tebl/RC1802-Cosmac-ELF/Gallery/1802_ui_d2.PNG

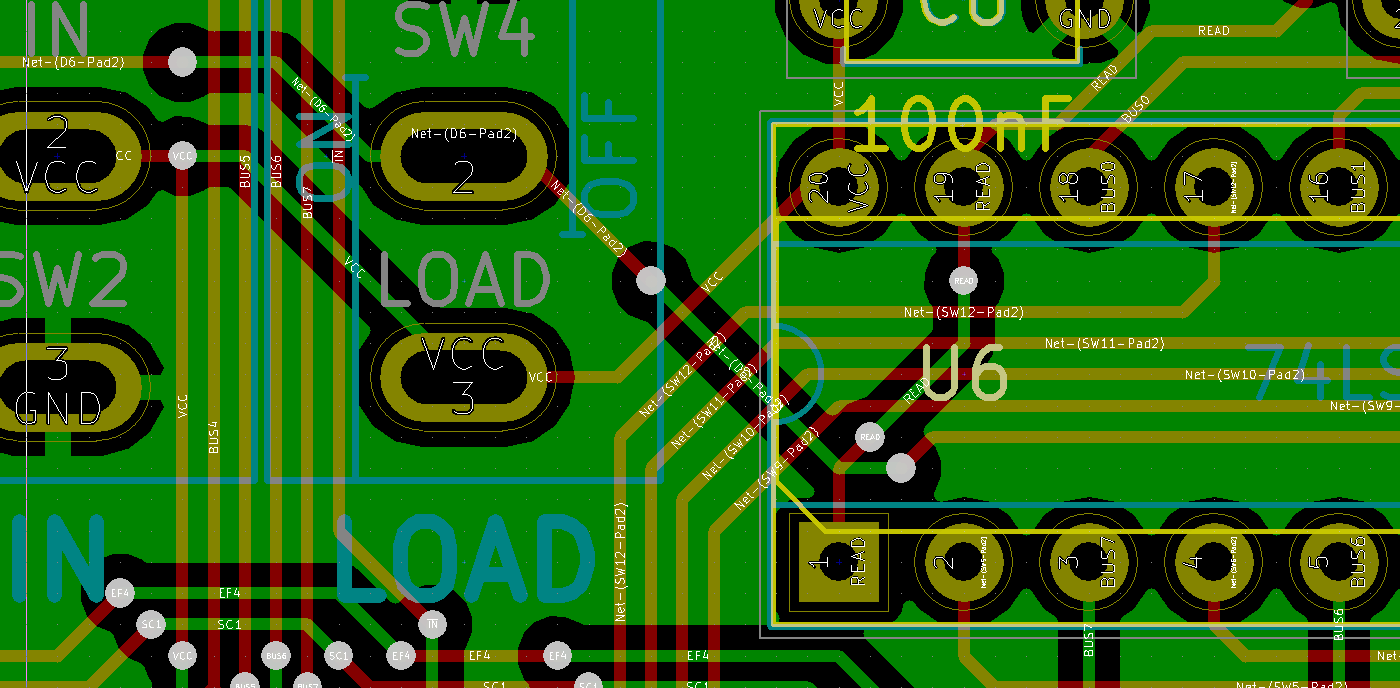
Gallery/1802_ui_d2.PNG
