tebl/RC1802-Cosmac-ELF/Gallery/Loopback_000.jpg

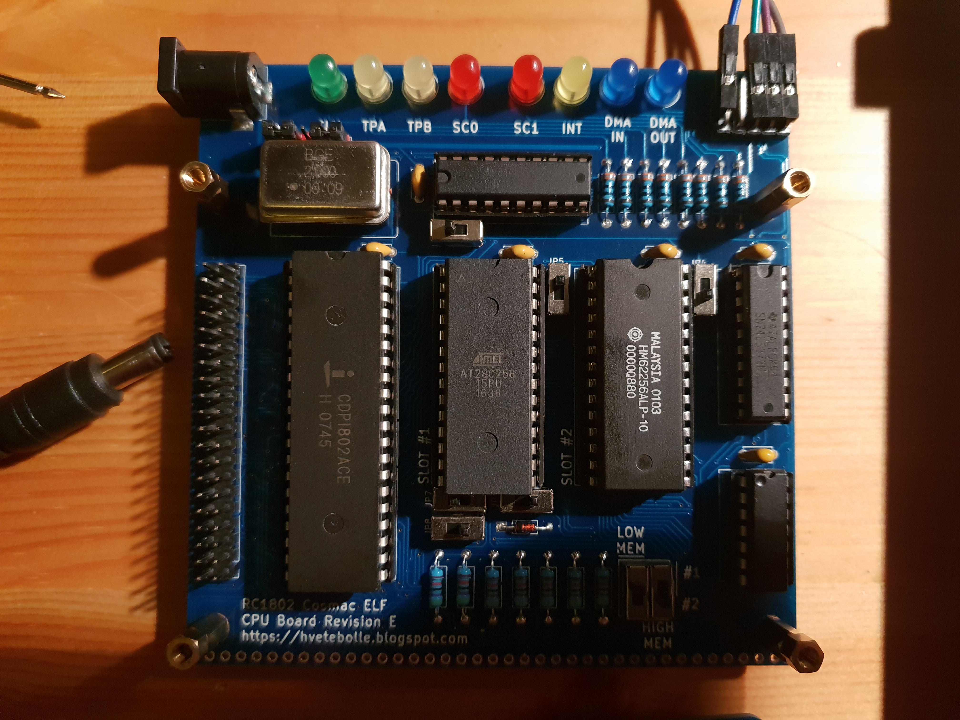
Gallery/Loopback_000.jpg
