tebl/RC1802-Cosmac-ELF/Gallery/Loopback_001.jpg

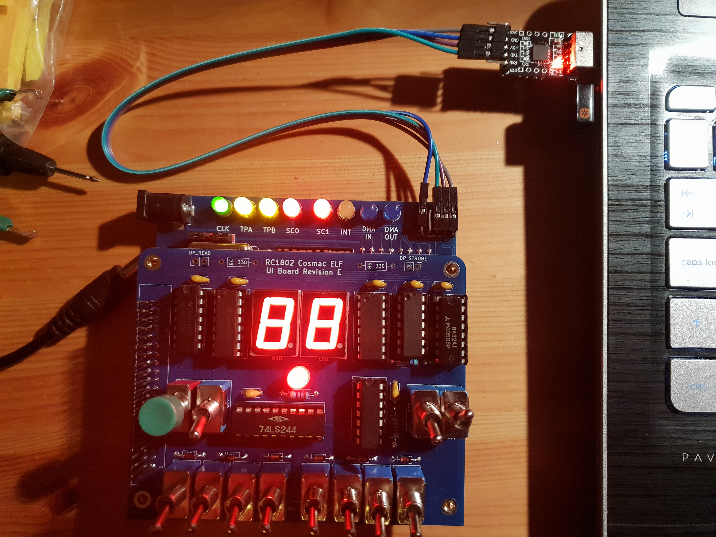
Gallery/Loopback_001.jpg
